hsmade/8bit-computer/ROM/programmer/include/firmware.h

const static byte FIRMWARE0[] PROGMEM = {
0xa2,
0xff,
0x9a,
0xa9,
0x00,
0x8d,
0x01,
0x50,
0xa9,
0x1f,
0x8d,
0x03,
0x50,
0xa9,
0x0b,
0x8d,
0x02,
0x50,
0xad,
0x01,
0x50,
0x29,
0x08,
0xf0,
0xf9,
0xad,
0x00,
0x50,
0x20,
0x22,
0x80,
0x4c,
0x12,
0x80,
0x8d,
0x00,
0x50,
0x48,
0xad,
0x01,
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
};
const byte FIRMWARE1[] PROGMEM = {
0x80,
};
const byte *const FIRMWARE[2] = { FIRMWARE0, FIRMWARE1 };
unsigned int FIRMWARESIZE = 32768;
